PWRFLcreative/Spore/firmware/Spore/wifi_config.h

/* Config.h
 * Git repo does not track this file, so you can safely store your credentials here!
 */
 
#ifndef WIFI_CONFIG_H
#define WIFI_CONFIG_H

#define WIFI_SSID     "your-ssid"       // replace with your wifi SSID
#define WIFI_PASSWORD "your-password"   // replace with your wifi password


#endif /* SETTINGS_H */
